Supermagnum/diplexer/highpass.asc

C1: cap; 43.00p
C3: cap; 24.00p
C4: cap; 24.00p
C5: cap; 24.00p
C6: cap; 24.00p
C7: cap; 24.00p
C9: cap; 30.00p
L1: ind; 62.00n
L2: ind; 75.00n
L3: ind; 62.00n
L4: ind; 62.00n
L6: ind; 62.00n
L8: ind; 56.00n
L10: ind; 100.0n
RL: res; 50
V1: voltage; ""; AC 1 0; Rser=50.00
Named nets: 0
.ac dec 1001 11.04Meg 172.5Meg
.net I(RL) V1
10th Order Chebyshev Highpass
Series First
Cutoff Frequency = 69 MHz
Passband Ripple = 0.10 dB
