Supermagnum/diplexer/lowpassfilter.asc

C2: cap; 91.00p
C4: cap; 110.0p
C6: cap; 110.0p
C8: cap; 110.0p
C10: cap; 62.00p
L1: ind; 160.0n
L3: ind; 270.0n
L5: ind; 270.0n
L7: ind; 270.0n
L9: ind; 220.0n
RL: res; 50
V1: voltage; ""; AC 1 0; Rser=50.00
Named nets: 0
.ac dec 1001 22.00Meg 343.8Meg
.net I(RL) V1
10th Order Chebyshev Lowpass
Series First
Cutoff Frequency = 55 MHz
Passband Ripple = 0.10 dB
